JuliusKlodt/TrackingSystem/Bericht/Bilder/Pictures/3D-prited stuff.jpeg

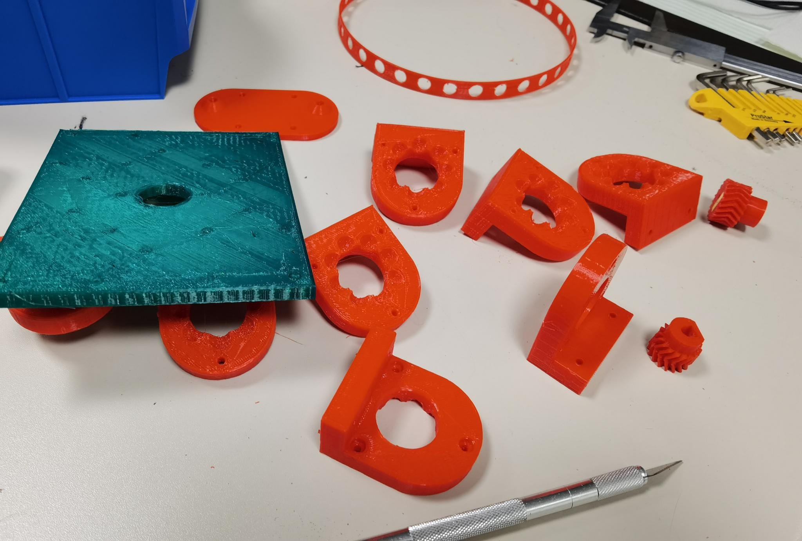
Bericht/Bilder/Pictures/3D-prited stuff.jpeg
