JuliusKlodt/TrackingSystem/Bericht/Bilder/Pictures/Arduino and Raspi.jpeg

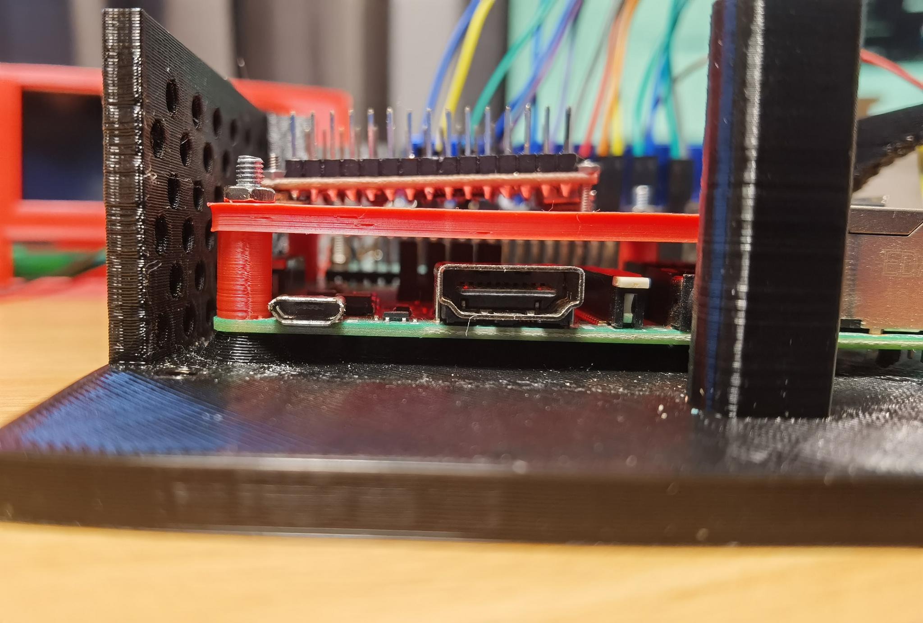
Bericht/Bilder/Pictures/Arduino and Raspi.jpeg
