JuliusKlodt/TrackingSystem/Bericht/Bilder/Pictures/Control-panel.jpeg

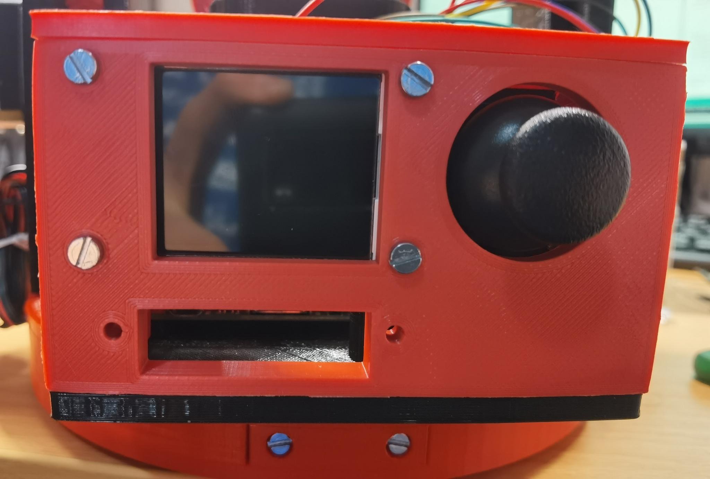
Bericht/Bilder/Pictures/Control-panel.jpeg
