JuliusKlodt/TrackingSystem/Software/UML-Diagramm.jpg

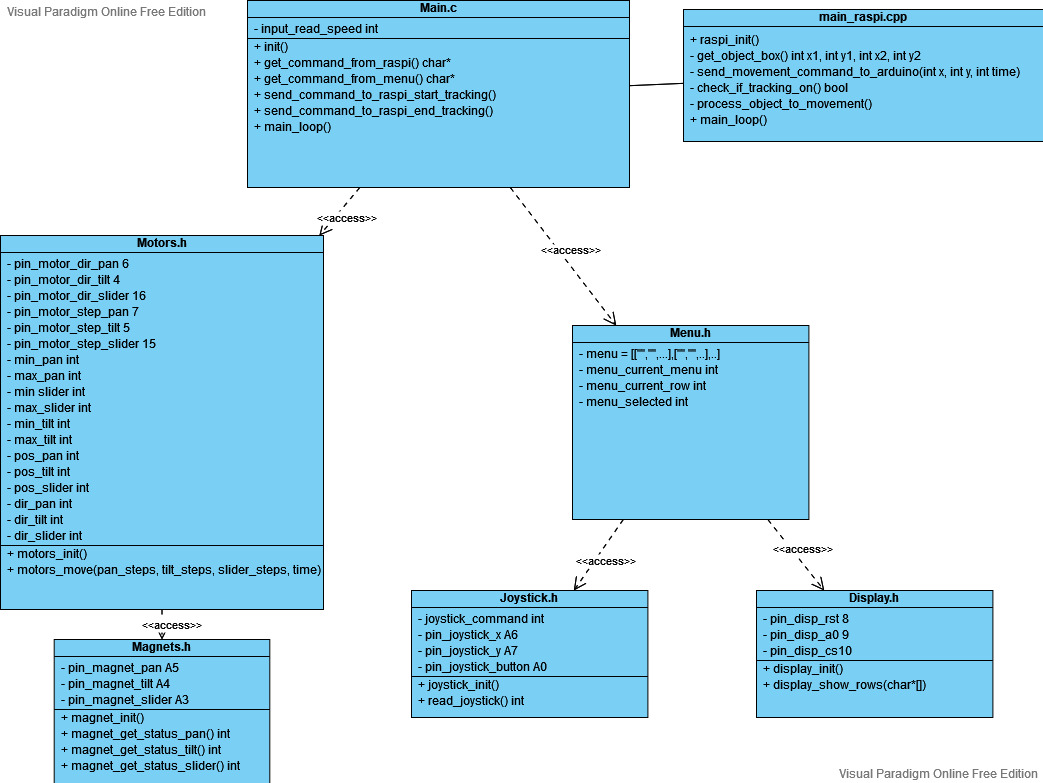
Software/UML-Diagramm.jpg
