JuliusKlodt/TrackingSystem/Hardware/STL Dateien/Kamerabefestigung.stl

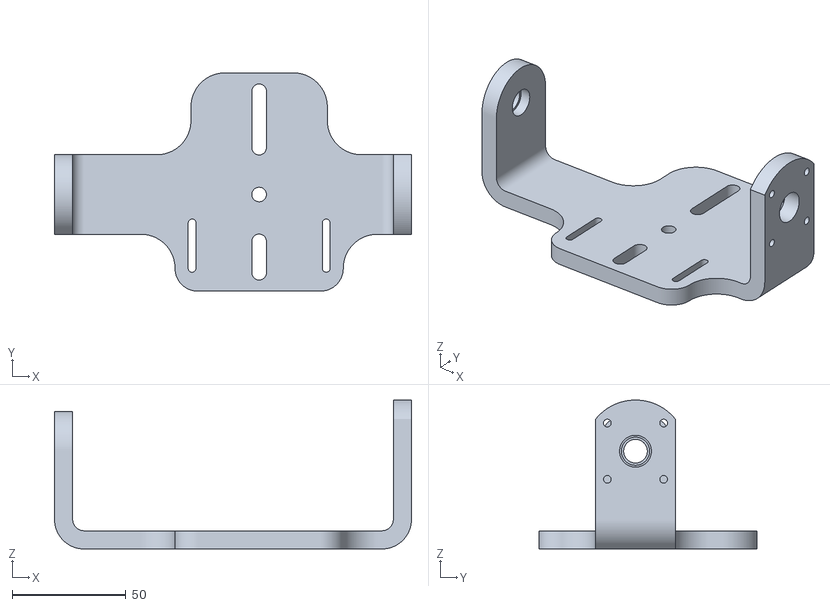
[picture p77: CAD file, 2022-02-16]
Hardware/STL Dateien/Kamerabefestigung.stl
157.0 x 96.0 x 65.5
