JuliusKlodt/TrackingSystem/Hardware/Zu druckende Teile/Abstandshalter mit Sensorhalterung.FCStd

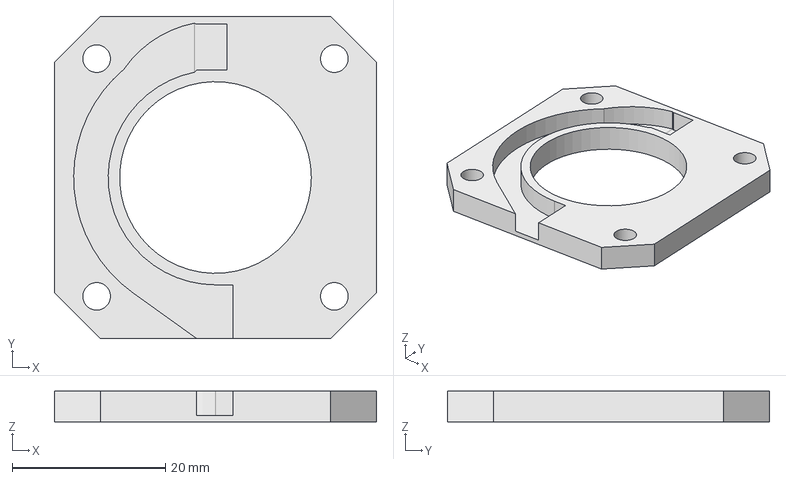
[picture p78: CAD file, 2022-02-16]
Hardware/Zu druckende Teile/Abstandshalter mit Sensorhalterung.FCStd
42.0 x 42.0 x 4.00 mm
