JuliusKlodt/TrackingSystem/Hardware/STL Dateien/Fuß - rechte Kamerabefestigung.stl

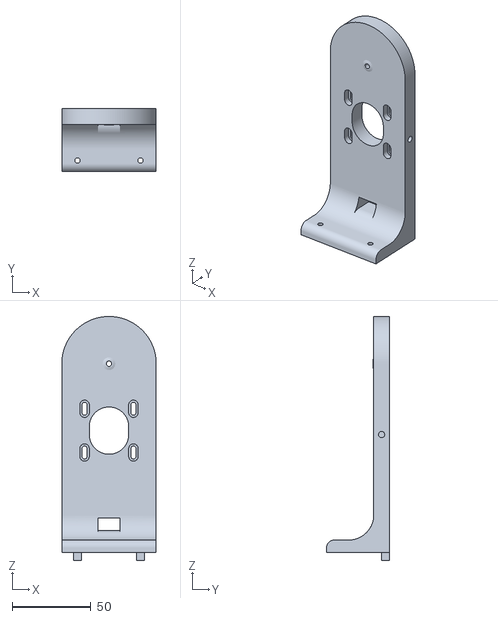
[picture p79: CAD file, 2022-02-16]
Hardware/STL Dateien/Fuß - rechte Kamerabefestigung.stl
60.0 x 40.0 x 155.0
