JuliusKlodt/TrackingSystem/Hardware/Zu druckende Teile/Linke Kamerahalterung.FCStd

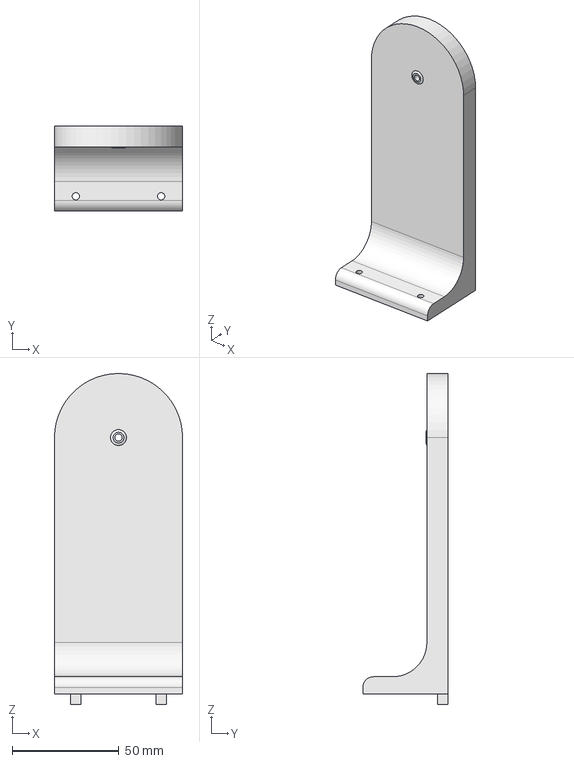
[picture p80: CAD file, 2022-02-16]
Hardware/Zu druckende Teile/Linke Kamerahalterung.FCStd
60.0 x 40.0 x 155.0 mm
