JuliusKlodt/TrackingSystem/Hardware/STL Dateien/Käfig für Elektronik - Joystickhalterung.stl

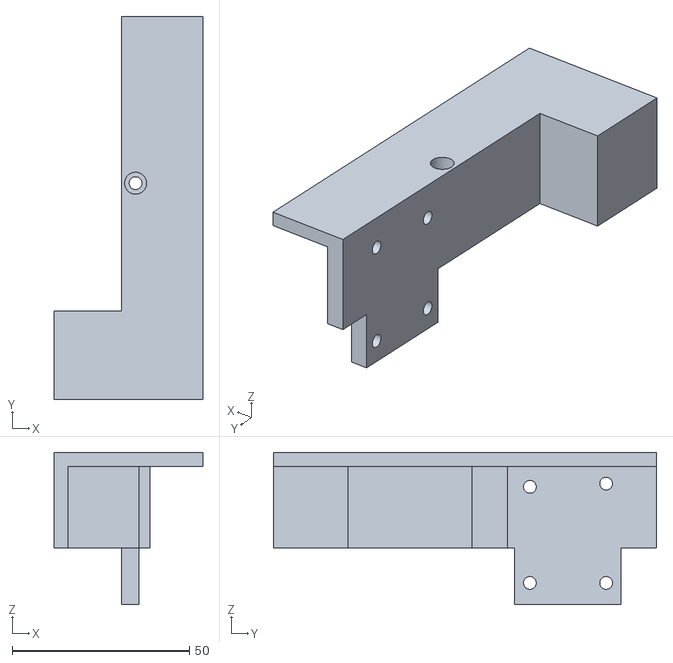
[picture p81: CAD file, 2022-02-16]
Hardware/STL Dateien/Käfig für Elektronik - Joystickhalterung.stl
42.0 x 108.0 x 43.0
