JuliusKlodt/TrackingSystem/Hardware/STL Dateien/Hauptplattform.stl

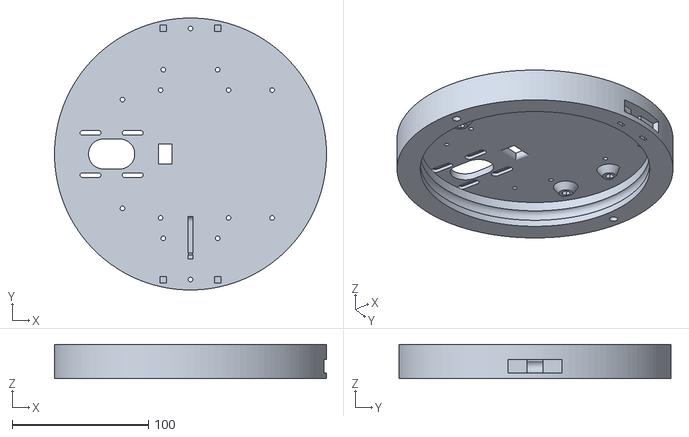
[picture p82: CAD file, 2022-02-16]
Hardware/STL Dateien/Hauptplattform.stl
200.0 x 199.9 x 25.0
