JuliusKlodt/TrackingSystem/Hardware/Zu druckende Teile/Motor und Umlenkrollenbefestigung.FCStd

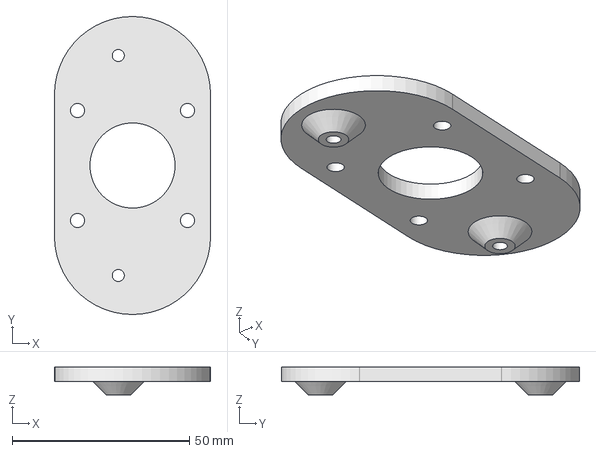
[picture p83: CAD file, 2022-02-16]
Hardware/Zu druckende Teile/Motor und Umlenkrollenbefestigung.FCStd
44.0 x 84.0 x 7.80 mm
