JuliusKlodt/TrackingSystem/Hardware/STL Dateien/Obere Platte für Slider.stl

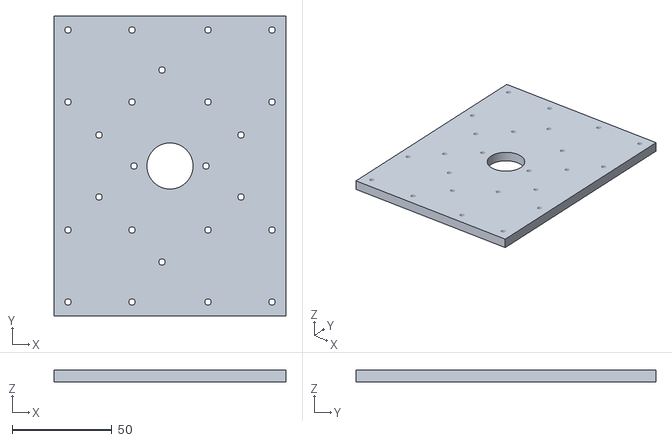
[picture p84: CAD file, 2022-02-16]
Hardware/STL Dateien/Obere Platte für Slider.stl
116.0 x 150.0 x 6.00
