JuliusKlodt/TrackingSystem/Hardware/Zu druckende Teile/Rohrverbinder.FCStd

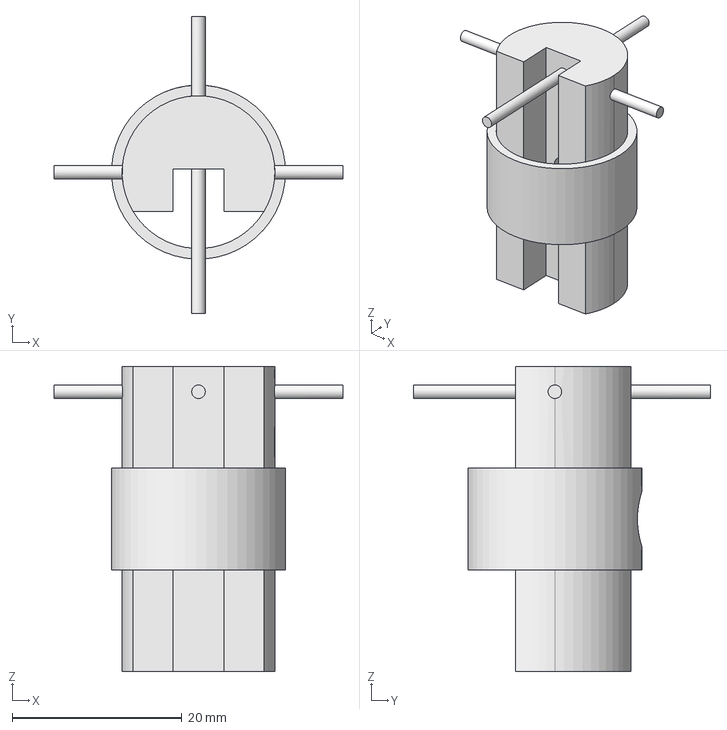
[picture p85: CAD file, 2022-02-16]
Hardware/Zu druckende Teile/Rohrverbinder.FCStd
34.0 x 35.0 x 36.0 mm
