JuliusKlodt/TrackingSystem/Hardware/Zu druckende Teile/17 Zahnrad für Plattformdrehung.FCStd

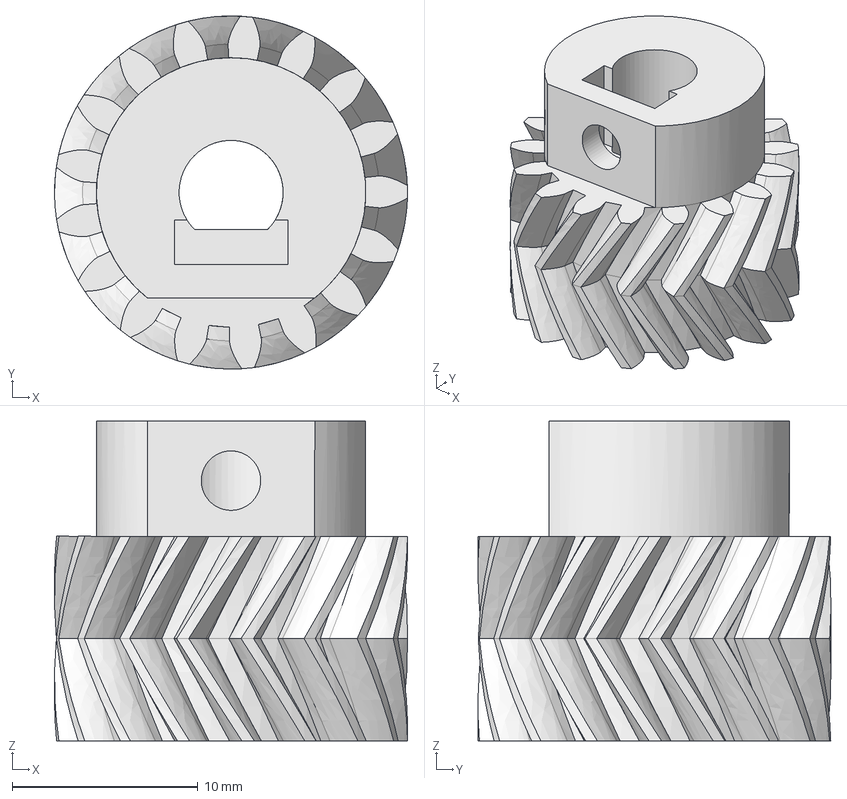
[picture p86: CAD file, 2022-02-16]
Hardware/Zu druckende Teile/17 Zahnrad für Plattformdrehung.FCStd
19.0 x 19.0 x 17.2 mm
