JuliusKlodt/TrackingSystem/Hardware/STL Dateien/64 Zahnrad für Kameradrehung.stl

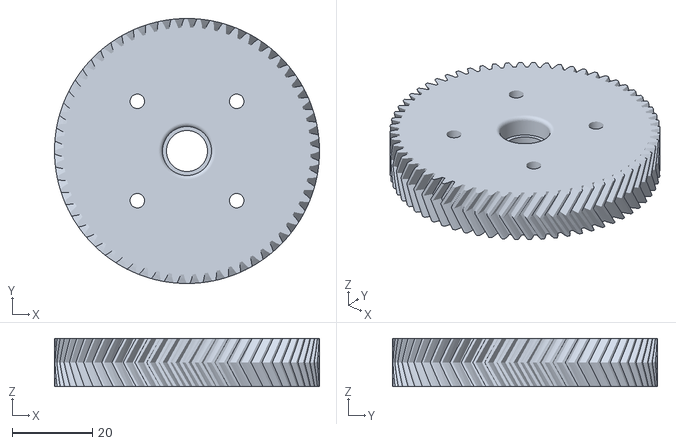
[picture p87: CAD file, 2022-02-16]
Hardware/STL Dateien/64 Zahnrad für Kameradrehung.stl
66.0 x 66.0 x 12.0
