JuliusKlodt/TrackingSystem/Hardware/STL Dateien/Motor und Umlenkrollenhalterung.stl

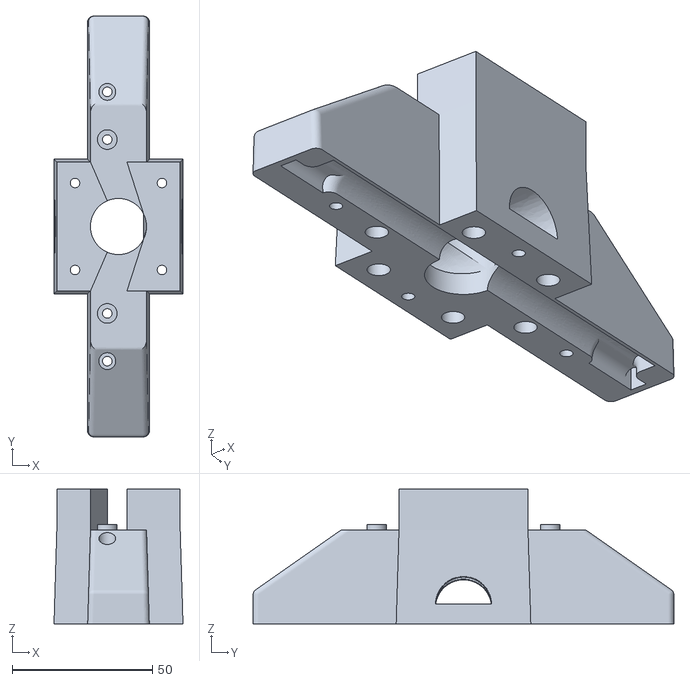
[picture p88: CAD file, 2022-02-16]
Hardware/STL Dateien/Motor und Umlenkrollenhalterung.stl
46.0 x 150.0 x 48.0
