JuliusKlodt/TrackingSystem/Hardware/Zu druckende Teile/Obere Platte für Slider.FCStd

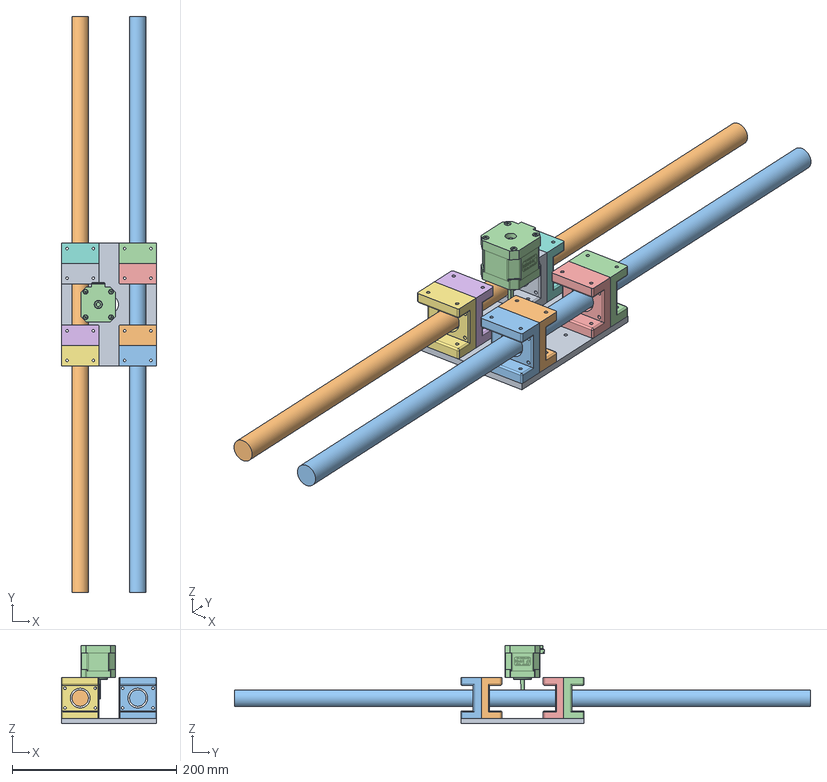
[picture p89: CAD file, 2021-12-14]
Hardware/Zu druckende Teile/Obere Platte für Slider.FCStd
116.0 x 700.0 x 95.0 mm
Obere Platte für Slider
Befestigungshälfte001
Befestigungshälfte
Befestigungshälfte002
Befestigungshälfte003
Befestigungshälfte004
Befestigungshälfte005
Befestigungshälfte007
Befestigungshälfte006
Zylinder
Zylinder001
Nema 17 Stepper Motor 42x42x40mm Tilt
