JuliusKlodt/TrackingSystem/Hardware/Zu druckende Teile/64 Zahnrad für Kameradrehung.FCStd

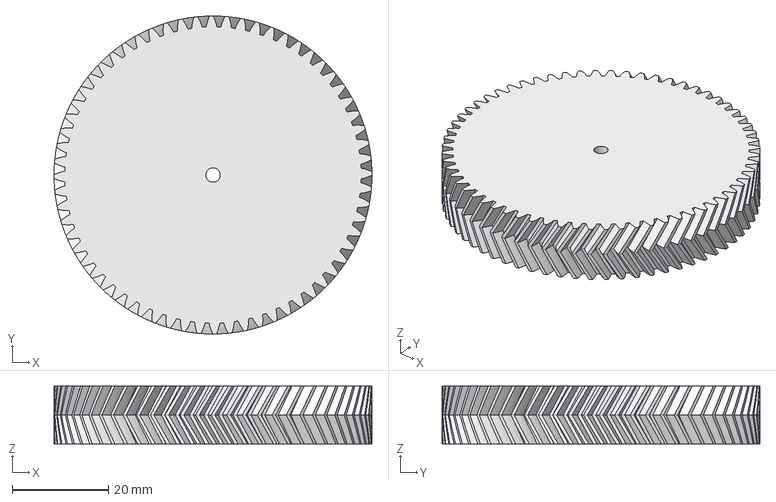
[picture p90: CAD file, 2021-12-05]
Hardware/Zu druckende Teile/64 Zahnrad für Kameradrehung.FCStd
66.0 x 66.0 x 12.0 mm
