JuliusKlodt/TrackingSystem/Hardware/STL Dateien/Stopfen HDMI.stl

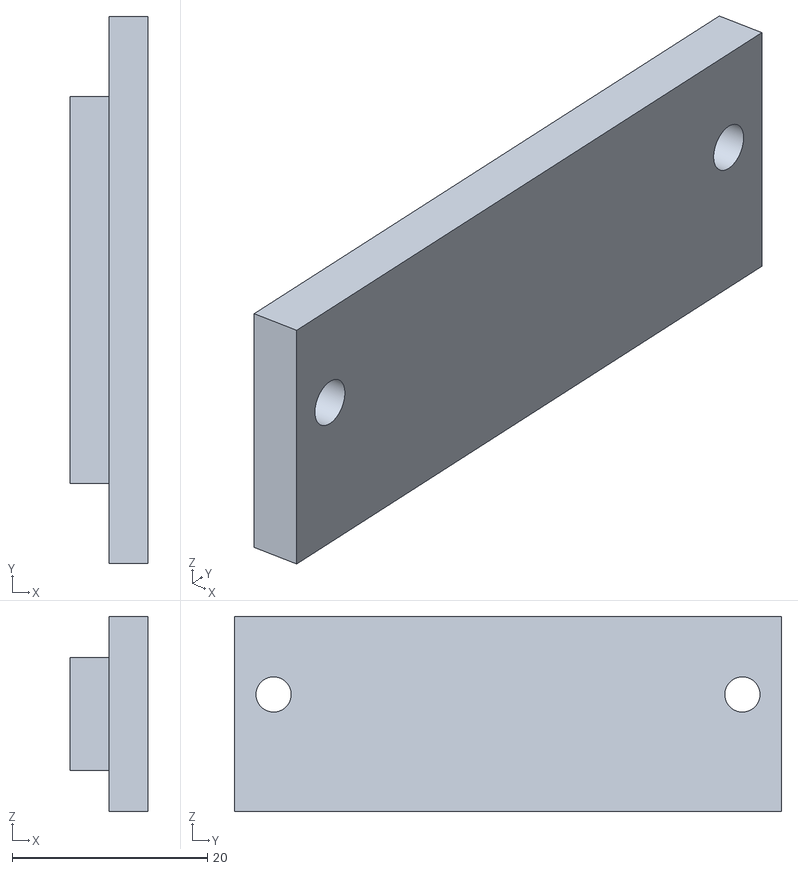
[picture p91: CAD file, 2022-02-16]
Hardware/STL Dateien/Stopfen HDMI.stl
8.00 x 56.0 x 20.0
