JuliusKlodt/TrackingSystem/Hardware/STL Dateien/Statische Basis mit innerem Zahnrad.stl

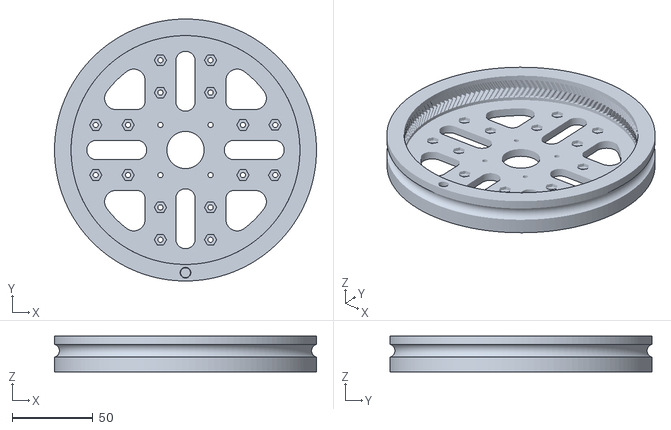
[picture p92: CAD file, 2022-01-11]
Hardware/STL Dateien/Statische Basis mit innerem Zahnrad.stl
162.0 x 161.9 x 22.0
