JuliusKlodt/TrackingSystem/Bericht/Bilder/Pictures/First pan-tilt assembly.jpeg

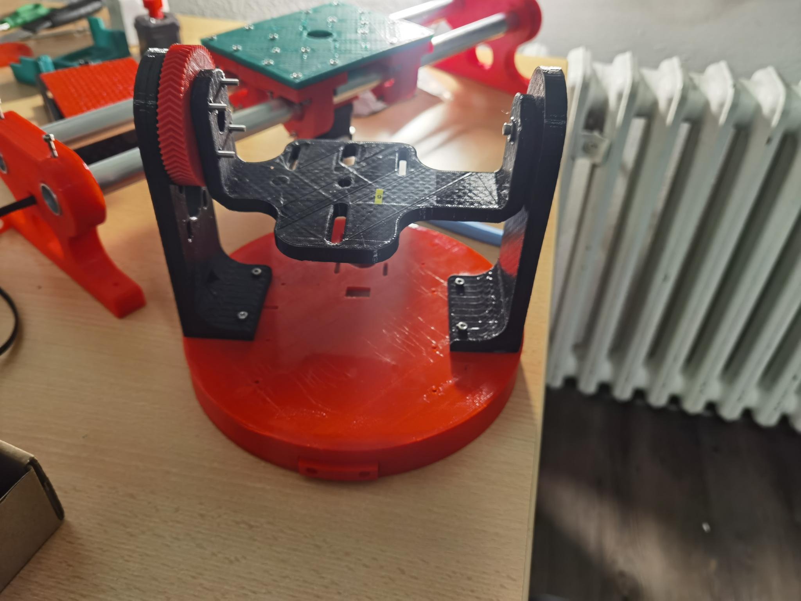
Bericht/Bilder/Pictures/First pan-tilt assembly.jpeg
